yosukev2/optical-modem-ish/hw/step01_power.kicad_sch

## KiCad design hw/step01_power.kicad_sch (2026-02-14, an earlier design)

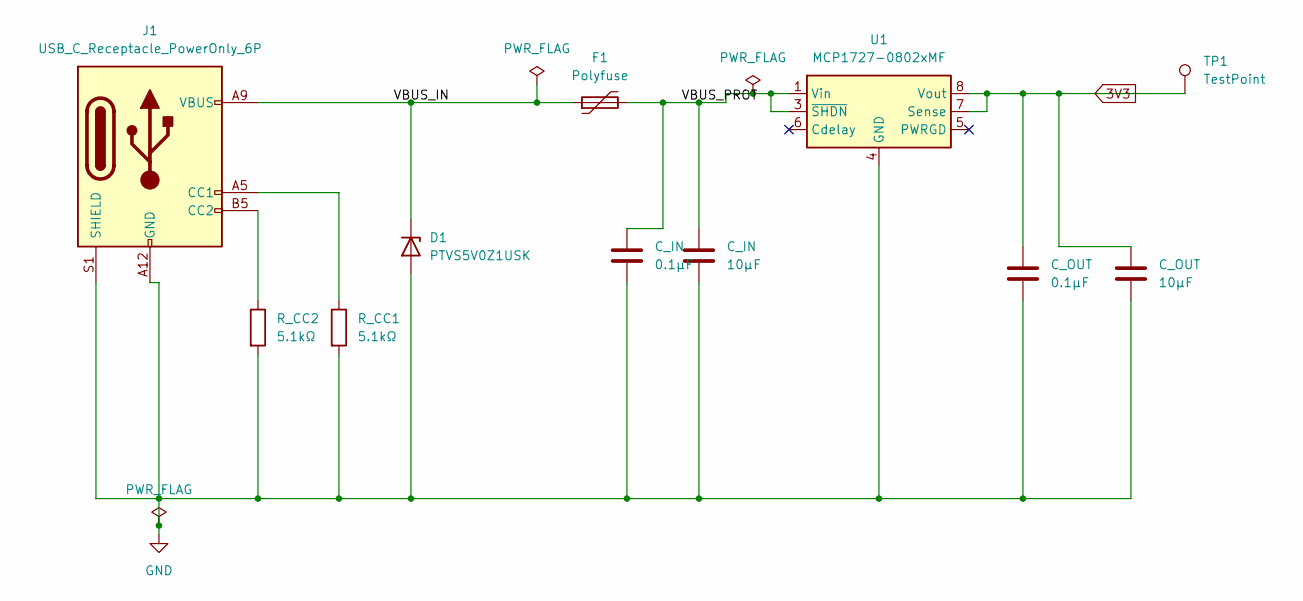
[picture p2: schematic step01_power.kicad_sch]

Parts:
C_IN: 0.1μF
C_OUT: 0.1μF
D1: PTVS5V0Z1USK; Nexperia_DSN1608-2_1.6x0.8mm
F1: Polyfuse
J1: USB_C_Receptacle_PowerOnly_6P
R_CC1, R_CC2: 5.1kΩ
TP1: TestPoint
U1: MCP1727-0802xMF; DFN-8-1EP_3x3mm_P0.65mm_EP1.55x2.4mm

Connections:
3V3: C_OUT.1, TP1.1, U1.7 (Sense), U1.8 (Vout)
GND: C_IN.2, C_OUT.2, D1.2 (A), J1.A12 (GND), J1.B12 (GND), J1.S1 (SHIELD), R_CC1.2, R_CC2.2, U1.4 (GND), U1.9 (GND)
unnamed: J1.A5 (CC1), R_CC1.1
unnamed: J1.B5 (CC2), R_CC2.1
VBUS_IN: D1.1 (K), F1.1, J1.A9 (VBUS), J1.B9 (VBUS)
VBUS_PROT: C_IN.1, F1.2, U1.1 (Vin), U1.2 (Vin), U1.3 (~SHDN)
