yosukev2/optical-modem-ish/fw/apps/blink/main.c

#include "pico/stdlib.h"

#ifndef PICO_DEFAULT_LED_PIN
#define PICO_DEFAULT_LED_PIN 25
#endif

int main() {
    const uint LED = PICO_DEFAULT_LED_PIN;

    gpio_init(LED);
    gpio_set_dir(LED, GPIO_OUT);

    while (true) {
        gpio_put(LED, 1);
        sleep_ms(250);
        gpio_put(LED, 0);
        sleep_ms(250);
    }
}
